domipapp/LIN-Driver-Linking/temalabor_usart/src/motor_vezerles.h

void setOut1(void);
void clearOut1(void);
void disableOut1(void);


void setOut2(void);
void clearOut2(void);
void disableOut2(void);


void setOut3(void);
void clearOut3(void);
void disableOut3(void);
